jp112sdl/HB-RF-MOD/Images/IMG_1773.jpg

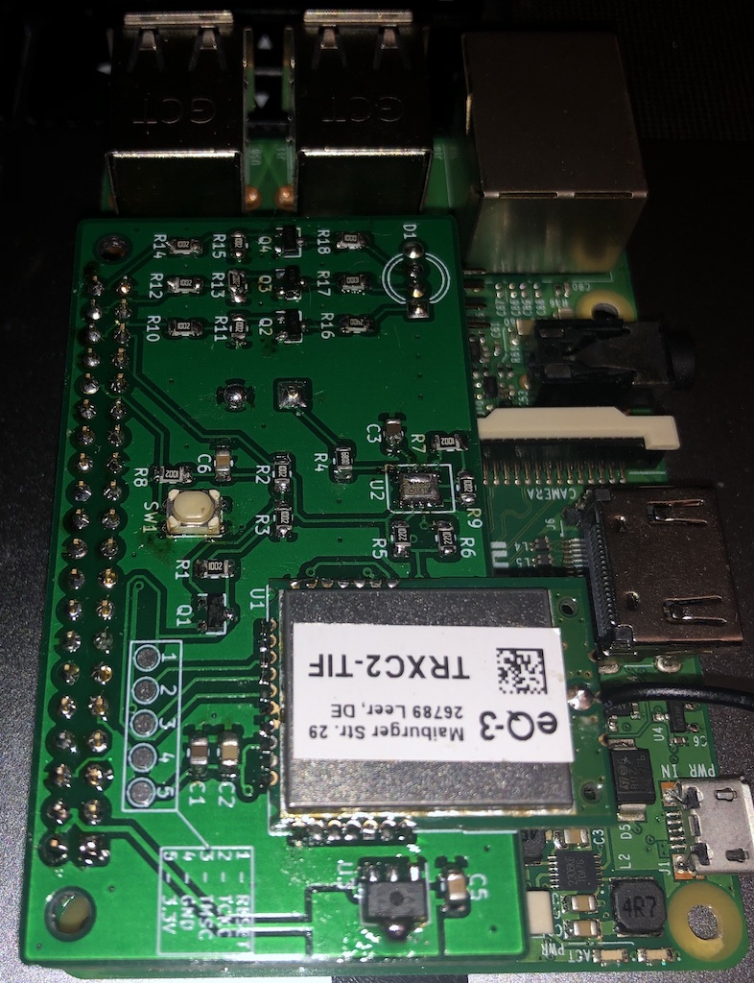
Images/IMG_1773.jpg
